Protocentral/HealthyPi/gui/healthypi_desktop/SpO2_cal.pde

//////////////////////////////////////////////////////////////////////////////////////////
//
//   SPO2_cal:
//      - This Class calculates the SpO2 value According to the PPG data received
//
//   Created : Balasundari, Aug 2016
//   
/////////////////////////////////////////////////////////////////////////////////////////

public class SPO2_cal
{
  float Vdc = 0;
  float Vac = 0;
  float spo2_cal_array[] = new float[pSize];

  float SPO2 = 0;

  ///////////////////////////////////////////////////////////////////////////
  //  
  //  To Calulate the Spo2 value any one of the following Emprical Formal are used:
  //    1. float SpO2 = 10.0002*(value)-52.887*(value) + 26.817*(value) + 98.293;
  //    2. float SpO2 =((0.81-0.18*(value))/(0.73+0.11*(value)));
  //    3. float SpO2=110-25*(value);
  //  In this Program, the 3rd formulae is used
  //
  //////////////////////////////////////////////////////////////////////////

  public void rawDataArray(float ir_array[], float red_array[], double ir_avg, double red_avg)
  {
    float RedAC = s.SPO2_Value(red_array);
    float IrAC = s.SPO2_Value(ir_array);
    float value = (RedAC/abs((float)red_avg))/(IrAC/abs((float)ir_avg));
    float SpO2=110-25*(value);
    SpO2 = (int)(SpO2 * 100);
    SpO2 = Math.round(SpO2/100);
    SP02.setText((SpO2+10)+"");
  }
  
  ////////////////////////////////////////////////////////////////////////////////////////////
  //  SPo2 Value is calculated by:
  //    * Calculate the square of the spo2 values and store it in the buffer
  //    * Sum of the values in the squared buffer is calculated.
  //    * This sum is sent to the main function
  //   
  ////////////////////////////////////////////////////////////////////////////////////////////

  public float SPO2_Value(float spo2_array[])
  {
    SPO2 = 0;
    int k = 0;
    for (int i = 50; i < spo2_array.length; i++)
    {
      spo2_cal_array[k++] = spo2_array[i] * spo2_array[i];
    }
    SPO2 = sum(spo2_cal_array, k);
    return (SPO2);
  }

  public float sum(float array[], int len)
  {
    float spo2 = 0;
    for (int p = 0; p < len; p++)
    {
      spo2 = spo2 + array[p];
    }
    Vac = (float)Math.sqrt(spo2/len);
    return Vac;
  }
}
